EFilomena/PonchoDeBiopotenciales/Firmware/inc/poncho_biopotenciales.h

/* Copyright 2016, Pablo Ridolfi
 * All rights reserved.
 *
 * This file is part of Workspace.
 *
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
 * 3. Neither the name of the copyright holder nor the names of its
 *    contributors may be used to endorse or promote products derived from this
 *    software without specific prior written permission.
 *
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
 */

#ifndef _PONCHO_BIOPOTENCIALES_H_
#define _PONCHO_BIOPOTENCIALES_H_

/** \addtogroup blink Bare-metal blink example
 ** @{ */

/*==================[inclusions]=============================================*/
#include "Drv_Devices.h"
#include "Drv_GPIO.h"

/*==================[cplusplus]==============================================*/

#ifdef __cplusplus
extern "C" {
#endif

/*==================[macros]=================================================*/

/*==================[typedef]================================================*/

/*==================[external data declaration]==============================*/

/*==================[external functions declaration]=========================*/

/** @brief main function
 * @return main function should never return
 */
int main(void);

/*==================[cplusplus]==============================================*/

#ifdef __cplusplus
}
#endif

/** @} doxygen end group definition */
/*==================[end of file]============================================*/
#endif /* #ifndef _PONCHO_BIOPOTENCIALES_H_ */
